holyelk/FYP-IEM/Ideation/Braille clock/clock16-servo/clock-16-output-servo_schem.jpg

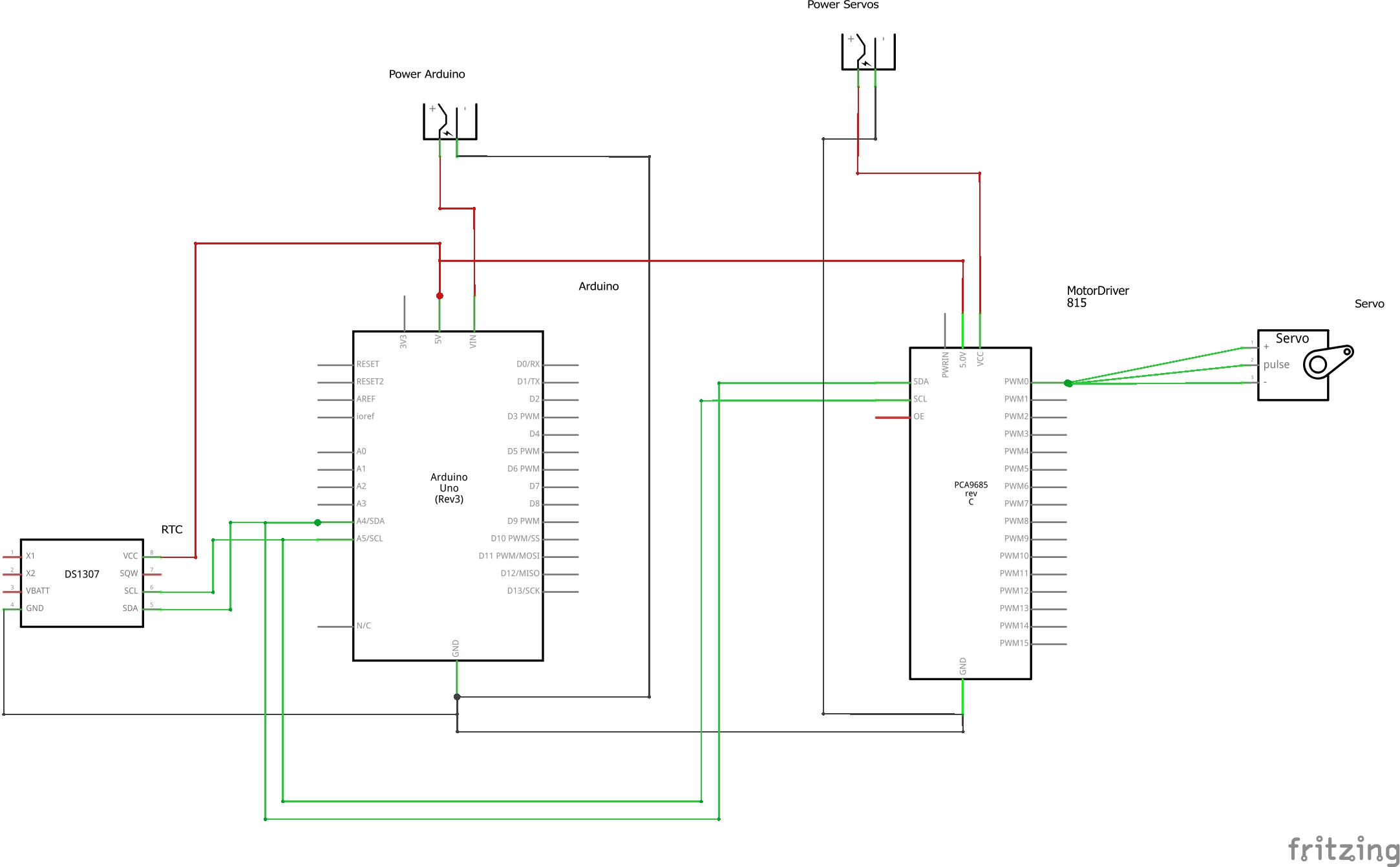
Ideation/Braille clock/clock16-servo/clock-16-output-servo_schem.jpg
